casa-ucl/ISS/physical device photos/into the gauge fusion 360 Small.jpeg

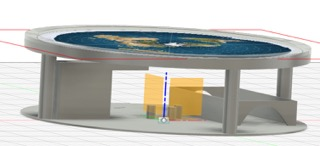
physical device photos/into the gauge fusion 360 Small.jpeg
