casa-ucl/ISS/physical device photos/map holder  Small.jpeg

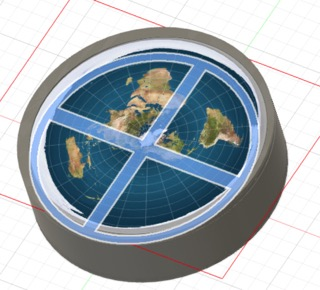
physical device photos/map holder Small.jpeg
