casa-ucl/ISS/physical device photos/3D printing Prusa Small.jpeg

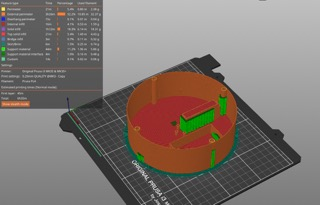
physical device photos/3D printing Prusa Small.jpeg
