casa-ucl/ISS/physical device photos/FINAL RESULT GAUGE INSIDE.jpeg

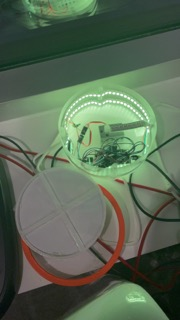
physical device photos/FINAL RESULT GAUGE INSIDE.jpeg
